ubiconet/NHLScoreboard/docs/components/periodmatrix.jpg

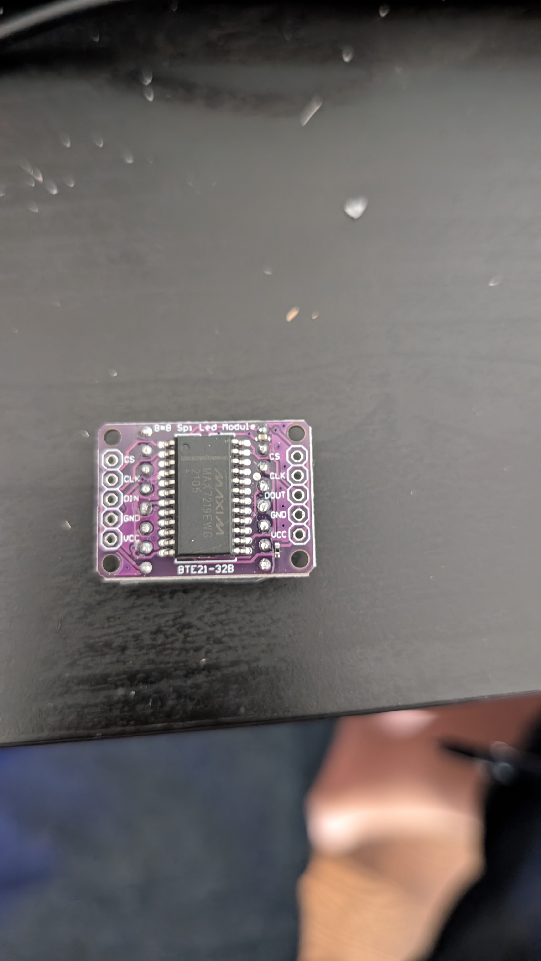
docs/components/periodmatrix.jpg
