ubiconet/NHLScoreboard/docs/components/scorematrix.jpg

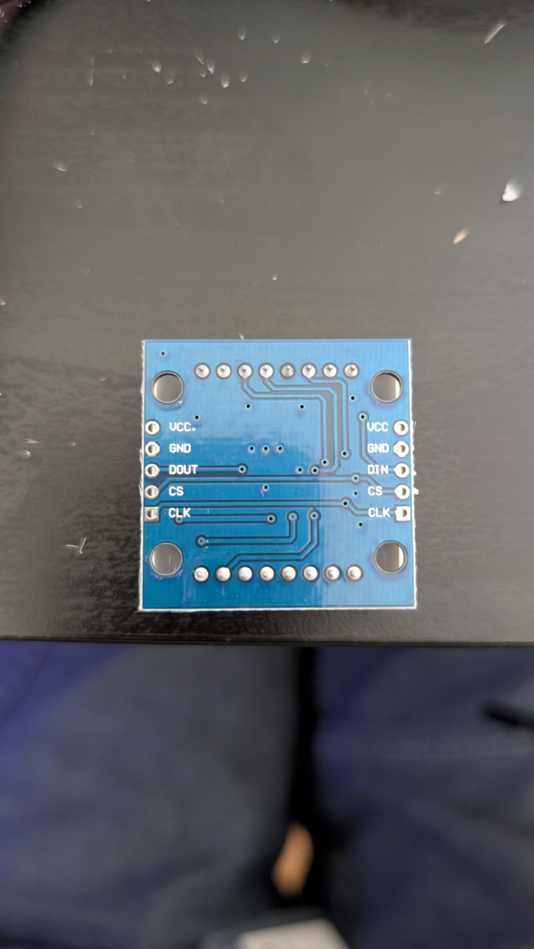
docs/components/scorematrix.jpg
