ubiconet/NHLScoreboard/docs/components/tft.jpg

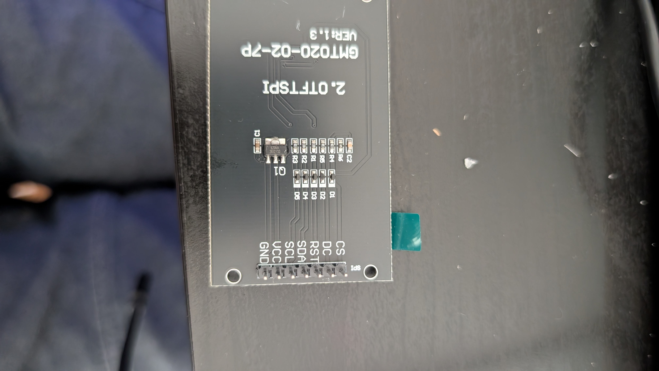
docs/components/tft.jpg
