ubiconet/NHLScoreboard/src/sports/nhl/nhl_data_task.cpp

#include <Arduino.h>
#include <ArduinoJson.h>
#include <WiFi.h>
#include <time.h>

#include "config.h"
#include "common/comms/network_service.h"
#include "common/comms/ota_update.h"
#include "common/data/time_util.h"
#include "nhl_client.h"
#include "nhl_renderer.h"
#include "nhl_state.h"

// Core-0 NHL data task: day-score poll (60 s), followed-game landing poll
// (5 s while live), ESPN news poll (30 min cache). Everything parses into
// POD snapshots and publishes through nhl_state; nothing here touches the
// display. Cadence rationale: docs/features/nhl-api/adr/0002.

namespace {

// ---- News cache: refresh at most every NHL_NEWS_CACHE_TTL_MS ----
uint32_t gLastNewsFetchAt   = 0;
uint32_t gLastNewsAttemptAt = 0;
uint32_t gNewsRetryInterval = NHL_NEWS_RETRY_MS;
NewsStory gCachedNews[MAX_NEWS_STORIES];

// ---- Schedule / landing pacing ----
uint32_t gLastScheduleAt = 0;
bool     gScheduleValid  = false;
uint32_t gLastLandingAt  = 0;

// ---- Week look-ahead cache (/v1/schedule, Mon-Sun) ----
JsonDocument gWeekDoc;       // filtered slate: gameWeek[] {date, games[]}
char     gWeekDate[11] = ""; // Monday the cache covers; "" = no cache
uint32_t gWeekFetchAt = 0;   // last refresh ATTEMPT (success or failure)

int periodLength(int period) { return period <= 3 ? 1200 : 300; }

int parseMmSs(const char* s) {
  int mm = 0, ss = 0;
  if (s == nullptr) return 0;
  sscanf(s, "%d:%d", &mm, &ss);
  return mm * 60 + ss;
}

// Game clock elapsed (seconds since puck drop) from the countdown clock:
// "period + seconds remaining in that period".
int gameElapsedFromClock(int period, int secRemaining) {
  int e = 0;
  for (int p = 1; p < period; ++p) e += periodLength(p);
  return e + (periodLength(period) - secRemaining);
}

// Game clock elapsed at an event's "timeInPeriod" stamp. Verified against
// play-by-play ground truth (timeInPeriod 00:45 <-> timeRemaining 19:15):
// the summary stamps ELAPSED time into the period, not the countdown.
int gameElapsedAtStamp(int period, const char* timeInPeriod) {
  int e = 0;
  for (int p = 1; p < period; ++p) e += periodLength(p);
  return e + parseMmSs(timeInPeriod);
}

GameSnapshot landingToSnapshot(JsonObjectConst d, long gameId) {
  GameSnapshot s{};
  s.valid = true;
  s.gameId = gameId;
  strlcpy(s.gameState, d["gameState"] | "?", sizeof(s.gameState));
  s.period = d["periodDescriptor"]["number"] | 0;
  strlcpy(s.periodType, d["periodDescriptor"]["periodType"] | "REG",
          sizeof(s.periodType));
  s.clockSec = d["clock"]["secondsRemaining"] | 0;
  s.clockRunning = d["clock"]["running"] | false;
  s.inIntermission = d["clock"]["inIntermission"] | false;
  s.awayTeamId = d["awayTeam"]["id"] | 0;
  s.homeTeamId = d["homeTeam"]["id"] | 0;
  strlcpy(s.awayAbbrev, d["awayTeam"]["abbrev"] | "??", sizeof(s.awayAbbrev));
  strlcpy(s.homeAbbrev, d["homeTeam"]["abbrev"] | "??", sizeof(s.homeAbbrev));
  s.awayScore = d["awayTeam"]["score"] | 0;
  s.homeScore = d["homeTeam"]["score"] | 0;
  s.awaySog = d["awayTeam"]["sog"] | 0;
  s.homeSog = d["homeTeam"]["sog"] | 0;

  // Scoring summary feeds two consumers in one pass: the latest-goal
  // record (goal announcement screen) and the per-period linescore
  // (goals counted per team per period group; multi-OT collapses into
  // the OT column, the shootout gets its own).
  NhlGoal latestGoal{};
  for (JsonObjectConst scoringPeriod :
       d["summary"]["scoring"].as<JsonArrayConst>()) {
    int pNum = scoringPeriod["periodDescriptor"]["number"] | 0;
    const char* pType =
        scoringPeriod["periodDescriptor"]["periodType"] | "";
    int col = -1;
    if (strcmp(pType, "SO") == 0) col = 4;
    else if (strcmp(pType, "OT") == 0 || pNum >= 4) col = 3;
    else if (pNum >= 1 && pNum <= 3) col = pNum - 1;
    for (JsonObjectConst goal :
         scoringPeriod["goals"].as<JsonArrayConst>()) {
      const char* team = goal["teamAbbrev"]["default"] | "";
      if (col >= 0 && team[0] != '\0') {
        if (strcmp(team, s.homeAbbrev) == 0) ++s.homePeriodGoals[col];
        else if (strcmp(team, s.awayAbbrev) == 0) ++s.awayPeriodGoals[col];
      }
      if ((goal["homeScore"] | -1) != s.homeScore ||
          (goal["awayScore"] | -1) != s.awayScore) {
        continue;
      }
      NhlGoal parsed{};
      parsed.eventId = goal["eventId"] | 0;
      parsed.homeScore = goal["homeScore"] | 0;
      parsed.awayScore = goal["awayScore"] | 0;
      parsed.scorer.playerId = goal["playerId"] | 0;
      parsed.scorer.number = goal["sweaterNumber"] | 0;
      strlcpy(parsed.scorer.name, goal["name"]["default"] | "",
              sizeof(parsed.scorer.name));
      strlcpy(parsed.teamAbbrev, team, sizeof(parsed.teamAbbrev));
      for (JsonObjectConst assist :
           goal["assists"].as<JsonArrayConst>()) {
        if (parsed.assistCount >= 2) break;
        NhlGoalPlayer& player = parsed.assists[parsed.assistCount++];
        player.playerId = assist["playerId"] | 0;
        player.number = assist["sweaterNumber"] | 0;
        strlcpy(player.name, assist["name"]["default"] | "",
                sizeof(player.name));
      }
      parsed.valid = parsed.scorer.playerId > 0 &&
                     parsed.teamAbbrev[0] != '\0';
      if (parsed.valid) latestGoal = parsed;
    }
  }
  s.latestGoal = latestGoal;
  s.otColumn = s.homePeriodGoals[3] > 0 || s.awayPeriodGoals[3] > 0 ||
               (s.period >= 4 && strcmp(s.periodType, "SO") != 0);
  s.soColumn = s.homePeriodGoals[4] > 0 || s.awayPeriodGoals[4] > 0 ||
               strcmp(s.periodType, "SO") == 0;

  // Three stars — the landing summary only populates these at or near
  // game end; until then the array is absent and the count stays 0.
  uint8_t stars = 0;
  for (JsonObjectConst star :
       d["summary"]["threeStars"].as<JsonArrayConst>()) {
    if (stars >= 3) break;
    NhlThreeStar& t = s.threeStars[stars++];
    strlcpy(t.name, star["name"]["default"] | "", sizeof(t.name));
    strlcpy(t.teamAbbrev, star["teamAbbrev"]["default"] | "",
            sizeof(t.teamAbbrev));
    t.number = star["sweaterNo"] | 0;
    t.goals = star["goals"] | 0;
    t.assists = star["assists"] | 0;
  }
  s.threeStarCount = stars;

  // Active penalties: the summary lists every penalty with its start
  // (period + elapsed stamp) and duration; a penalty is active while
  // start + duration > now on the game clock. During an intermission the
  // feed's clock carries the BREAK countdown, not period time — deriving
  // elapsed from it would burn penalty time during the pause, so penalty
  // math anchors to the last in-play clock reading instead (penalty
  // clocks stop with play, like the real thing).
  static int sPlayPeriod = 1, sPlayClockSec = 1200;
  if (!s.inIntermission && s.period > 0) {
    sPlayPeriod = s.period;
    sPlayClockSec = s.clockSec;
  }
  int now = gameElapsedFromClock(s.inIntermission ? sPlayPeriod
                                                  : (s.period > 0 ? s.period : 1),
                                 s.inIntermission ? sPlayClockSec : s.clockSec);
  int cnt = 0;
  for (JsonObjectConst grp : d["summary"]["penalties"].as<JsonArrayConst>()) {
    int pPeriod = grp["periodDescriptor"]["number"] | 0;
    for (JsonObjectConst pen : grp["penalties"].as<JsonArrayConst>()) {
      int start = gameElapsedAtStamp(pPeriod > 0 ? pPeriod : 1,
                                     pen["timeInPeriod"] | "0:00");
      int dur = pen["duration"] | 2;
      int remain = start + dur * 60 - now;
      if (remain <= 0) continue;
      const char* team = pen["teamAbbrev"]["default"] | "";
      if (strcmp(team, s.homeAbbrev) == 0) ++s.homePenaltyCount;
      else ++s.awayPenaltyCount;
      if (cnt < 4) {
        NhlPenalty& p = s.penalties[cnt++];
        strlcpy(p.teamAbbrev, team, sizeof(p.teamAbbrev));
        strlcpy(p.lastName,
                pen["committedByPlayer"]["lastName"]["default"] | "",
                sizeof(p.lastName));
        p.number = pen["committedByPlayer"]["sweaterNumber"] | 0;
        strlcpy(p.desc, pen["descKey"] | "penalty", sizeof(p.desc));
        p.remainSec = remain;
        p.durMin = dur;
      }
    }
  }
  s.penaltyCount = cnt;
  return s;
}

void fetchNewsIfDue(bool online) {
  uint32_t now = millis();
  bool fresh = gLastNewsFetchAt != 0 &&
               (now - gLastNewsFetchAt) < NHL_NEWS_CACHE_TTL_MS;
  bool throttled = gLastNewsFetchAt == 0 && gLastNewsAttemptAt != 0 &&
                   (now - gLastNewsAttemptAt) < gNewsRetryInterval;
  if (!online || fresh || throttled || portalEngaged()) return;
  gLastNewsAttemptAt = now;

  JsonDocument doc;
  if (!fetchEspnNhlNews(doc)) {
    gNewsRetryInterval = min<uint32_t>(gNewsRetryInterval * 2, 300000UL);
    return;
  }
  gNewsRetryInterval = NHL_NEWS_RETRY_MS;
  gLastNewsFetchAt = now;

  size_t n = 0;
  for (JsonObjectConst a : doc["articles"].as<JsonArrayConst>()) {
    if (n >= MAX_NEWS_STORIES) break;
    const char* h = a["headline"] | "";
    const char* d2 = a["description"] | "";
    if (h[0] == '\0') continue;
    strlcpy(gCachedNews[n].headline, h, sizeof(gCachedNews[n].headline));
    strlcpy(gCachedNews[n].description, d2, sizeof(gCachedNews[n].description));
    NewsSlotUpdate slot{};
    slot.index = n;
    strlcpy(slot.headline, h, sizeof(slot.headline));
    strlcpy(slot.description, d2, sizeof(slot.description));
    publishNewsStory(slot);
    ++n;
  }
  setNewsStoryCount(n);
  DBG_PRINTF("[ESPN] applied %u news stories\n", (unsigned)n);
}

void fetchScheduleIfDue(bool online) {
  if (!online || portalEngaged()) return;
  if (!timeIsSynced()) return;  // no trustworthy local date yet
  uint32_t now = millis();
  uint32_t interval = gScheduleValid ? NHL_SCHEDULE_POLL_INTERVAL_MS
                                     : NHL_SCHEDULE_RETRY_MS;
  if (gLastScheduleAt != 0 && (now - gLastScheduleAt) < interval) return;
  gLastScheduleAt = now;

  char date[11];
  time_t t = time(nullptr);
  tm lt = {};
  localtime_r(&t, &lt);
  if (strftime(date, sizeof(date), "%Y-%m-%d", &lt) == 0) return;

  JsonDocument doc;
  if (!fetchNhlDayScore(doc, date)) {
    gScheduleValid = false;
    return;
  }
  gScheduleValid = true;

  ScheduleSnapshot snap{};
  size_t n = 0;
  auto appendGames = [&](JsonObjectConst src) {
    for (JsonObjectConst g : src["games"].as<JsonArrayConst>()) {
      if (n >= 26) break;
      long id = g["id"] | 0;
      bool dup = false;
      for (size_t k = 0; k < n; ++k)
        if (snap.games[k].gameId == id) { dup = true; break; }
      if (dup) continue;
      NhlDayGame& o = snap.games[n++];
      o.gameId = id;
      strlcpy(o.awayAbbrev, g["awayTeam"]["abbrev"] | "??", sizeof(o.awayAbbrev));
      strlcpy(o.homeAbbrev, g["homeTeam"]["abbrev"] | "??", sizeof(o.homeAbbrev));
      o.awayTeamId = g["awayTeam"]["id"] | 0;
      o.homeTeamId = g["homeTeam"]["id"] | 0;
      o.awayScore = g["awayTeam"]["score"] | 0;
      o.homeScore = g["homeTeam"]["score"] | 0;
      strlcpy(o.gameState, g["gameState"] | "?", sizeof(o.gameState));
      strlcpy(o.startUtc, g["startTimeUTC"] | "", sizeof(o.startUtc));
    }
  };
  appendGames(doc.as<JsonObjectConst>());

  // Upcoming-games look-ahead: one /v1/schedule call covers the Mon-Sun
  // week containing today. The cache only refreshes on TTL (6 h) or when
  // the week rolls over — future-day states never change, and today's
  // half of the upcoming doc below always comes from the fresh day-score
  // fetch above. Failed refreshes retry on their own spacing.
  {
    time_t monday = t - ((lt.tm_wday + 6) % 7) * 24 * 60 * 60;
    tm md = {};
    localtime_r(&monday, &md);
    char mondayStr[11];
    if (strftime(mondayStr, sizeof(mondayStr), "%Y-%m-%d", &md) > 0) {
      uint32_t sinceFetch = millis() - gWeekFetchAt;
      bool need = strcmp(gWeekDate, mondayStr) != 0 ||
                  sinceFetch > NHL_WEEK_SCHEDULE_TTL_MS;
      bool mayTry = gWeekFetchAt == 0 ||
                    sinceFetch >= NHL_WEEK_SCHEDULE_RETRY_MS;
      if (need && mayTry) {
        gWeekFetchAt = millis();
        if (fetchNhlWeekSchedule(gWeekDoc, date)) {
          strlcpy(gWeekDate,
                  gWeekDoc["gameWeek"][0]["date"] | mondayStr,
                  sizeof(gWeekDate));
        } else {
          gWeekDate[0] = '\0';
          gWeekDoc.clear();
        }
      }
    }
  }
  bool weekValid = gWeekDate[0] != '\0';

  // The upcoming-games cache the waiting screen walks: today's fresh
  // games, then every later day of the cached week — so the carousel's
  // per-team cards and the upcoming list span a full seven days.
  JsonDocument upcomingDoc;
  JsonArray merged = upcomingDoc["games"].to<JsonArray>();
  for (JsonObjectConst g : doc["games"].as<JsonArrayConst>()) merged.add(g);
  if (weekValid) {
    for (JsonObjectConst day : gWeekDoc["gameWeek"].as<JsonArrayConst>()) {
      if (strcmp(day["date"] | "", date) <= 0) continue;  // today merged fresh
      appendGames(day);  // snapshot/ticker look-ahead (dedup + 26 cap)
      for (JsonObjectConst g : day["games"].as<JsonArrayConst>()) {
        merged.add(g);
      }
    }
  } else {
    // Week fetch unavailable (fresh boot in a bad TLS window): fall back
    // to the old one-day look-ahead so tomorrow's card still shows.
    time_t tmrw = t + 24 * 60 * 60;
    tm td = {};
    localtime_r(&tmrw, &td);
    char tdate[11];
    if (strftime(tdate, sizeof(tdate), "%Y-%m-%d", &td) > 0) {
      JsonDocument tdoc;
      if (fetchNhlDayScore(tdoc, tdate)) {
        appendGames(tdoc.as<JsonObjectConst>());
        for (JsonObjectConst g : tdoc["games"].as<JsonArrayConst>()) {
          merged.add(g);
        }
      }
    }
    if (n == 0) {
      const char* nextDate = doc["nextDate"] | "";
      if (nextDate[0] != '\0') {
        JsonDocument ndoc;
        if (fetchNhlDayScore(ndoc, nextDate)) {
          appendGames(ndoc.as<JsonObjectConst>());
          for (JsonObjectConst g : ndoc["games"].as<JsonArrayConst>()) {
            merged.add(g);
          }
        }
      }
    }
  }

  // After local midnight the API's "today" no longer contains the previous
  // date's late games — some still in progress. Merge yesterday's slate
  // during the overlap window so live selection never drops a game (and a
  // followed game stays visible through its postgame grace).
  if (lt.tm_hour < 8) {
    time_t yst = t - 24 * 60 * 60;
    tm yd = {};
    localtime_r(&yst, &yd);
    char ydate[11];
    if (strftime(ydate, sizeof(ydate), "%Y-%m-%d", &yd) > 0) {
      JsonDocument ydoc;
      if (fetchNhlDayScore(ydoc, ydate)) appendGames(ydoc.as<JsonObjectConst>());
    }
  }

  snap.count = n;
  snap.valid = true;
  nhl_data::publishSchedule(snap);
  publishUpcomingScheduleJson(upcomingDoc.as<JsonObjectConst>());
}

// ---- Division standings (waiting-screen pages) ----
uint32_t gLastStandingsAt = 0;
bool     gStandingsValid = false;

void fetchStandingsIfDue(bool online) {
  if (!online || portalEngaged()) return;
  if (!timeIsSynced()) return;
  uint32_t now = millis();
  uint32_t interval = gStandingsValid ? NHL_STANDINGS_TTL_MS
                                      : NHL_STANDINGS_RETRY_MS;
  if (gLastStandingsAt != 0 && (now - gLastStandingsAt) < interval) return;
  gLastStandingsAt = now;

  char date[11];
  time_t t = time(nullptr);
  tm lt = {};
  localtime_r(&t, &lt);
  if (strftime(date, sizeof(date), "%Y-%m-%d", &lt) == 0) return;

  JsonDocument doc;
  if (!fetchNhlStandings(doc, date)) {
    gStandingsValid = false;
    return;
  }
  // Group into the four divisions in first-seen order (the feed orders
  // rows by league sequence, which is the within-division rank).
  StandingsSnapshot snap{};
  for (JsonObjectConst r : doc["standings"].as<JsonArrayConst>()) {
    const char* div = r["divisionName"] | "";
    const char* ab = r["teamAbbrev"]["default"] | "";
    if (div[0] == '\0' || ab[0] == '\0') continue;
    int d = -1;
    for (int k = 0; k < 4; ++k) {
      if (snap.count[k] == 0) continue;
      if (strncmp(snap.divisionName[k], div, sizeof(snap.divisionName[0])) == 0) {
        d = k;
        break;
      }
    }
    if (d < 0) {
      for (int k = 0; k < 4; ++k) {
        if (snap.count[k] == 0) { d = k; break; }
      }
      if (d < 0) break;  // more than four divisions — take the first four
      strlcpy(snap.divisionName[d], div, sizeof(snap.divisionName[0]));
    }
    if (snap.count[d] >= 8) continue;
    StandingsRow& row = snap.rows[d][snap.count[d]++];
    strlcpy(row.abbrev, ab, sizeof(row.abbrev));
    row.wins = r["wins"] | 0;
    row.losses = r["losses"] | 0;
    row.otLosses = r["otLosses"] | 0;
    row.points = r["points"] | 0;
  }
  snap.valid = snap.count[0] > 0;
  gStandingsValid = snap.valid;
  if (snap.valid) updateStandings(snap);
}

// Landing failure backoff: a dead keep-alive socket means every retry
// pays a fresh TLS handshake, and this AP's flood protection refuses
// exactly those for a window after a burst — retrying every 5 s flat
// prolongs the outage (the same reasoning as the schedule backoff,
// ADR-0002). Doubles per consecutive failure, capped, reset on success.
uint32_t gLandingRetryInterval = NHL_LIVE_POLL_INTERVAL_MS;

void fetchLandingIfDue(bool online) {
  static long lastGameId = 0;
  static int lastHomeScore = -1;
  static int lastAwayScore = -1;
  long id = getActiveGameId();
  if (id <= 0 || !online || portalEngaged()) return;
  uint32_t now = millis();
  if (gLastLandingAt != 0 && (now - gLastLandingAt) < gLandingRetryInterval) {
    return;
  }
  gLastLandingAt = now;

  JsonDocument doc;
  if (!fetchNhlGameLanding(doc, id)) {
    gLandingRetryInterval *= 2;
    if (gLandingRetryInterval > NHL_LANDING_RETRY_MAX_MS) {
      gLandingRetryInterval = NHL_LANDING_RETRY_MAX_MS;
    }
    return;
  }
  gLandingRetryInterval = NHL_LIVE_POLL_INTERVAL_MS;
  GameSnapshot game = landingToSnapshot(doc.as<JsonObjectConst>(), id);
  bool scoreIncreased = id == lastGameId &&
      (game.homeScore > lastHomeScore || game.awayScore > lastAwayScore);
  lastGameId = id;
  lastHomeScore = game.homeScore;
  lastAwayScore = game.awayScore;
  if (scoreIncreased && game.latestGoal.valid) {
    bool needsRoster = game.latestGoal.scorer.number <= 0;
    for (int i = 0; i < game.latestGoal.assistCount; ++i) {
      needsRoster = needsRoster || game.latestGoal.assists[i].number <= 0;
    }
    if (needsRoster) {
      nhl_data::publishGame(game);
      if (fetchNhlGameRoster(doc, id)) {
        for (JsonObjectConst player : doc["rosterSpots"].as<JsonArrayConst>()) {
          int playerId = player["playerId"] | 0;
          int number = player["sweaterNumber"] | 0;
          if (playerId == game.latestGoal.scorer.playerId) {
            game.latestGoal.scorer.number = number;
          }
          for (int i = 0; i < game.latestGoal.assistCount; ++i) {
            if (playerId == game.latestGoal.assists[i].playerId) {
              game.latestGoal.assists[i].number = number;
            }
          }
        }
        nhl_data::publishGame(game);
      }
      return;
    }
  }
  nhl_data::publishGame(game);
}

void nhlDataTaskLoop(void*) {
  // Online-since tracking for the OTA boot gate/pacing below.
  static uint32_t sOnlineSince = 0;
  while (true) {
    if (isOnline()) {
      if (sOnlineSince == 0) sOnlineSince = millis();
    } else {
      sOnlineSince = 0;
    }
    bool online = sOnlineSince != 0;
    uint32_t onlineFor = online ? millis() - sOnlineSince : 0;

    // OTA self-update service: check for a newer GitHub release each pass
    // (it paces itself — boot-only automatic checks plus the portal's
    // on-demand request). While a download is in flight this loop does
    // nothing else, and the feed fetches below must not start until the
    // boot check has run: its TLS handshake needs the pristine boot heap
    // (see otaBootGateReached in common/comms/ota_update.cpp). This wiring
    // existed in the MLB data task and was lost in the NHL port — the
    // updater was dead code until it was restored.
    serviceOtaUpdates(onlineFor);
    if (otaUpdateInProgress()) {
      vTaskDelay(pdMS_TO_TICKS(100));
      continue;
    }
    if (!otaBootGateReached(onlineFor)) {
      vTaskDelay(pdMS_TO_TICKS(50));
      continue;
    }

    fetchScheduleIfDue(online);
    fetchStandingsIfDue(online);
    fetchLandingIfDue(online);
    fetchNewsIfDue(online);
    vTaskDelay(pdMS_TO_TICKS(250));
  }
}

}  // namespace

void startNhlDataTask() {
  xTaskCreatePinnedToCore(nhlDataTaskLoop, "nhl_data", 12288, nullptr, 1,
                          nullptr, 0);
}
