ubiconet/NHLScoreboard/src/sports/nhl/nhl_client.h

#pragma once

#include <Arduino.h>
#include <ArduinoJson.h>

// NHL feed endpoints + JSON filters (core 0 only). Transport lives in
// common/comms/http_fetcher; the NHL web API is HTTPS-only, so these calls
// ride the shared TLS session (endpoints/payload sizes documented in
// docs/features/nhl-api/README.md).

// Day slate for a local date ("YYYY-MM-DD") from /v1/score/{date} (~42 KB,
// filtered). Keeps per-game: id, gameType, gameState, startTimeUTC,
// home/away {id, abbrev, score}.
bool fetchNhlDayScore(JsonDocument& doc, const char* dateStr);

// Mon-Sun week containing dateStr from /v1/schedule/{date} (~85 KB raw,
// ~13.5 KB filtered). Keeps gameWeek[] {date, games[] {id, gameState,
// startTimeUTC, home/away {id, abbrev}}} — the look-ahead source for the
// upcoming-games carousel.
bool fetchNhlWeekSchedule(JsonDocument& doc, const char* dateStr);

// Division standings from /v1/standings/{date} (~51 KB raw). Keeps per
// team: abbrev, divisionName, wins, losses, otLosses, points, sequence.
bool fetchNhlStandings(JsonDocument& doc, const char* dateStr);

// Live-game summary from /v1/gamecenter/{id}/landing (~11 KB, filtered):
// gameState, periodDescriptor, clock, team score/sog, penalty summary.
bool fetchNhlGameLanding(JsonDocument& doc, long gameId);

// Filtered roster jersey numbers from /v1/gamecenter/{id}/play-by-play.
// Requested only when a live-game score increases and the landing goal
// summary does not supply the scorer's sweater number.
bool fetchNhlGameRoster(JsonDocument& doc, long gameId);

// News headlines from ESPN (plain HTTP — see the News section of the API
// doc for why the RSS host lost to the api host).
bool fetchEspnNhlNews(JsonDocument& doc, int limit = 10);
