ubiconet/NHLScoreboard/src/common/hal/count_leds.h

#pragma once

#include <Arduino.h>

// Seven discrete status LEDs wired as three bar-graph counters of 3/2/2
// lamps. On the NHL build they read balls (3) / strikes (2) / outs (2);
// the driver itself only knows "counter A/B/C" — the sport layer supplies
// the pin map and passes its own counts.
//
// Pin order for initCountLeds():
//   pins[0..2] = counter A, least-significant lamp first (balls 1..3)
//   pins[3..4] = counter B (strikes 1..2)
//   pins[5..6] = counter C (outs 1..2)

void initCountLeds(const int pins[7]);
// Lights the first `countA/countB/countC` lamps of each counter; values are
// clamped by construction (>= comparisons), extra lamps stay dark.
void setCountLeds(uint8_t countA, uint8_t countB, uint8_t countC);

// TEST ONLY: cycles each LED on for 0.5 s, one at a time, then clears.
void runCountLedTestLoop();
